jiristanglica/pingpong-score-counter/src/display/src/Display.h

#ifndef Display_h
#define Display_h

#include <avr/pgmspace.h>
#include <MD_MAX72xx.h>
#include <SPI.h>

// Numeric Font Matrix (Arranged as 7x font data + 1x kerning data)
PROGMEM const unsigned char font5x7[] = {
    B00000000,  //Space (Char 0x20)
    B00000000,
    B00000000,
    B00000000,
    B00000000,
    B00000000,
    B00000000,
    4,

    B10000000,  //!
    B10000000,
    B10000000,
    B10000000,
    B00000000,
    B00000000,
    B10000000,
    2,

    B10100000,  //"
    B10100000,
    B10100000,
    B00000000,
    B00000000,
    B00000000,
    B00000000,
    4,

    B01010000,  //#
    B01010000,
    B11111000,
    B01010000,
    B11111000,
    B01010000,
    B01010000,
    6,

    B00100000,  //$
    B01111000,
    B10100000,
    B01110000,
    B00101000,
    B11110000,
    B00100000,
    6,

    B11000000,  //%
    B11001000,
    B00010000,
    B00100000,
    B01000000,
    B10011000,
    B00011000,
    6,

    B01100000,  //&
    B10010000,
    B10100000,
    B01000000,
    B10101000,
    B10010000,
    B01101000,
    6,

    B11000000,  //'
    B01000000,
    B10000000,
    B00000000,
    B00000000,
    B00000000,
    B00000000,
    3,

    B00100000,  //(
    B01000000,
    B10000000,
    B10000000,
    B10000000,
    B01000000,
    B00100000,
    4,

    B10000000,  //)
    B01000000,
    B00100000,
    B00100000,
    B00100000,
    B01000000,
    B10000000,
    4,

    B00000000,  //*
    B00100000,
    B10101000,
    B01110000,
    B10101000,
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
    B00000000,
    B00000000,
    B00000000,
    5
};

#define HARDWARE_TYPE MD_MAX72XX::FC16_HW
#define MAX_DEVICES 4

#define CLK_PIN   13  // or SCK
#define DATA_PIN  11  // or MOSI
#define CS_PIN    10  // or SS

class Display {
private:
    int totalSegments;
    int scrollPos = 32;

    MD_MAX72XX mx = MD_MAX72XX(HARDWARE_TYPE, CS_PIN, MAX_DEVICES);

public:
    Display(int numDevices = 1);

    void init();

    void clear();

    void setLed(int row, int col, int status);

    void printChar(char currentChar, int startCol = 0);

    void printText(char text[], int startCol = 0);

    void scrollText(char text[], int speed = 35);

    void resetScrollPosition();
};

#endif
